ElectroTechnique/TSynth-Teensy4.1/TSynth/effect_envelope.cpp

/* Audio Library for Teensy 3.X
 * Portions Copyright (c) 2017, Paul Stoffregen, paul@pjrc.com
 * Portions Copyright (c) 2021 Vince R. Pearson
 *
 * Development of this audio library was funded by PJRC.COM, LLC by sales of
 * Teensy and Audio Adaptor boards.  Please support PJRC's efforts to develop
 * open source software by purchasing Teensy or other PJRC products.
 *
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
 * THE SOFTWARE IS PROVIDED "AS IS", WITHOUT WARRANTY OF ANY KIND, EXPRESS OR
 * IMPLIED, INCLUDING BUT NOT LIMITED TO THE WARRANTIES OF MERCHANTABILITY,
 * FITNESS FOR A PARTICULAR PURPOSE AND NONINFRINGEMENT. IN NO EVENT SHALL THE
 * AUTHORS OR COPYRIGHT HOLDERS BE LIABLE FOR ANY CLAIM, DAMAGES OR OTHER
 * LIABILITY, WHETHER IN AN ACTION OF CONTRACT, TORT OR OTHERWISE, ARISING FROM,
 * OUT OF OR IN CONNECTION WITH THE SOFTWARE OR THE USE OR OTHER DEALINGS IN
 * THE SOFTWARE.
 */

#include <Arduino.h>
#include "effect_envelope.h"


#define RELEASE_BIAS 256 // based on a 1.31 fixed point integer. This is the level below zero that is the release target and causes the output to go to zero earlier. Otherwise it can take a relatively long time.
// Difference equation for exponential envelope.
#define FORCED_RELEASE_BIAS 0x1000000 // empirically determined with forced release time constant to attain ~5ms between forced release and next attack.
// Form 1 for attack stage: y(n+1) = k1*y(n)+kx using unsigned S1.30 fixed point format
#define EXP_ENV_FILT1(k,y,x) ((uint32_t)(((uint64_t)(y)*(k))>>30)+(uint32_t)(x))
// Form 2 for remaining stages: y(n+1) = k1*(y(n)-x(n))+x(n) using unsigned S1.30 fixed point format
#define EXP_ENV_FILT2(k,y,x) ((((int64_t)(k)*(int64_t)(y-x))>>30)+(x))
#define YSUM2MULT(x) ((x)>>14)

void AudioEffectEnvelopeTS::noteOn(void)
{
  __disable_irq();
  if(release_forced_count==0)
    state=STATE_IDLE;
  switch(state)
  {

    case STATE_IDLE:
    case STATE_IDLE_NEXT:
      // In a corner case, where the state becomes STATE_IDLE EXACTLY at the end of an update(),
	  // AND noteOn() is called before the next update() occurs, AND delay_count is non-zero, 
	  // AND the exponential envelope shape is in use, exp_count will have a stale value 
	  // of 2^32-1 and the delay becomes about 9 days. So duplicate some code here - it
	  // might be possible to move it instead
      exp_count=((uint32_t)(delay_count))*8;
      ysum=0;
	  
      count=delay_count;
      if(count>0)
      {
        state=STATE_DELAY;
        inc_hires=0;
      }
      else
      {
        state=STATE_ATTACK;
        count=attack_count;
      inc_hires = 0x40000000 / (int32_t)count;
      }
      break;    
    case STATE_DELAY:
    case STATE_HOLD:
    case STATE_ATTACK:
    case STATE_DECAY:
    case STATE_SUSTAIN:
    case STATE_SUSTAIN_FAST_CHANGE:
    case STATE_RELEASE:
      state=STATE_FORCED;
      count=release_forced_count;
      inc_hires=(-mult_hires)/(int32_t)count;
    case STATE_FORCED:
      break;
    default:
      state=STATE_RELEASE;
      break;
  }
  __enable_irq();
}

void AudioEffectEnvelopeTS::noteOff(void)
{
  __disable_irq();
  switch(state)
  {
    case STATE_IDLE:
    case STATE_IDLE_NEXT:
    case STATE_DELAY:
      state=STATE_IDLE;
      break;
    default:
      state = STATE_RELEASE;
      count = release_count;
      inc_hires = (-mult_hires) / (int32_t)count;
  }
  __enable_irq();
}

void AudioEffectEnvelopeTS::update(void)
{
  audio_block_t *block;
  uint32_t *p, *end;
  uint32_t sample12, sample34, sample56, sample78, tmp1, tmp2;
  uint32_t exp_mult[8];

  block = receiveWritable();
  if (!block) return;
  if (state == STATE_IDLE) {
    release(block);
    return;
  }
  p = (uint32_t *)(block->data);
  end = p + AUDIO_BLOCK_SAMPLES/2;
  if(env_type==-128)
  { // Original AudioEffectEnvelope class linear envelope.
    while (p < end) {
      // we only care about the state when completing a region
      if (count == 0) {
        if (state == STATE_ATTACK) {
          count = hold_count;
          if (count > 0) {
            state = STATE_HOLD;
            mult_hires = 0x40000000;
            inc_hires = 0;
          } else {
            state = STATE_DECAY;
            count = decay_count;
            inc_hires = (sustain_mult - 0x40000000) / (int32_t)count;
          }
          continue;
        } else if (state == STATE_HOLD) {
          state = STATE_DECAY;
          count = decay_count;
          inc_hires = (sustain_mult - 0x40000000) / (int32_t)count;
          continue;
        } else if (state == STATE_DECAY) {
          state = STATE_SUSTAIN;
          count = 0xFFFF;
          mult_hires = sustain_mult;
          inc_hires = 0;
        } else if (state == STATE_SUSTAIN) {
          count = 0xFFFF;
        } else if (state == STATE_RELEASE) {
          state = STATE_IDLE;
          while (p < end) {
            *p++ = 0;
            *p++ = 0;
            *p++ = 0;
            *p++ = 0;
          }
          break;
        } else if (state == STATE_FORCED) {
          mult_hires = 0;
          count = delay_count;
          if (count > 0) {
            state = STATE_DELAY;
            inc_hires = 0;
          } else {
            state = STATE_ATTACK;
            count = attack_count;
            inc_hires = 0x40000000 / (int32_t)count;
          }
        } else if (state == STATE_DELAY) {
          state = STATE_ATTACK;
          count = attack_count;
          inc_hires = 0x40000000 / count;
          continue;
        }
        else
        {
          state=STATE_IDLE; // If in some unused state switching back into linear mode, set to known state that linear mode uses.
          count=delay_count;
        }
      }

      int32_t mult = mult_hires >> 14;
      int32_t inc = inc_hires >> 17;
      // process 8 samples, using only mult and inc (16 bit resolution)
      sample12 = *p++;
      sample34 = *p++;
      sample56 = *p++;
      sample78 = *p++;
      p -= 4;
      mult += inc;
      tmp1 = signed_multiply_32x16b(mult, sample12);
      mult += inc;
      tmp2 = signed_multiply_32x16t(mult, sample12);
      sample12 = pack_16b_16b(tmp2, tmp1);
      mult += inc;
      tmp1 = signed_multiply_32x16b(mult, sample34);
      mult += inc;
      tmp2 = signed_multiply_32x16t(mult, sample34);
      sample34 = pack_16b_16b(tmp2, tmp1);
      mult += inc;
      tmp1 = signed_multiply_32x16b(mult, sample56);
      mult += inc;
      tmp2 = signed_multiply_32x16t(mult, sample56);
      sample56 = pack_16b_16b(tmp2, tmp1);
      mult += inc;
      tmp1 = signed_multiply_32x16b(mult, sample78);
      mult += inc;
      tmp2 = signed_multiply_32x16t(mult, sample78);
      sample78 = pack_16b_16b(tmp2, tmp1);
      *p++ = sample12;
      *p++ = sample34;
      *p++ = sample56;
      *p++ = sample78;
      // adjust the long-term gain using 30 bit resolution (fix #102)
      // https://github.com/PaulStoffregen/Audio/issues/102
      mult_hires += inc_hires;
      count--;
    }
  }
  else  //Exponential ADSR Vince R. Pearson
  {
    uint16_t i;
    while (p < end) 
    {
      for(i=0;i<8;i++)
      {
        switch(state)
        {
          case STATE_IDLE:
            // Since delay counts may not necessarily start at aligned boundaries of 8 samples,
            // the loop count has to be multiplied by 8
            // and counted down in the for loop, not in the while loop.
            exp_count=((uint32_t)(delay_count))*8;
            ysum=0;
            state=STATE_IDLE_NEXT; // Do this so reinitialization is only done once at every idle state.
            // Falls through to STATE_IDLE_NEXT
            
          case STATE_IDLE_NEXT:
            break; //ysum is zero here
            
          case STATE_DELAY:
            if(exp_count--) break; // ysum is zero here
            state=STATE_ATTACK;
            break;
            
          case STATE_ATTACK:
            ysum=EXP_ENV_FILT1(attack_k,ysum,attack_target);
            if(ysum>=EXP_ENV_ONE)  
            {   // The maximum 32 bit value of the envelope has been reached.
              ysum=EXP_ENV_ONE;
              if(hold_count)
              {
                exp_count=((uint32_t)hold_count)*8;
                state=STATE_HOLD;
              }
              else 
              {
                state=STATE_DECAY;
                exp_count=((uint32_t)delay_count)*8; // Only used to arbitrarioly define where sustain begins.
              }
            }
            break;
            
          case STATE_HOLD:
            if((exp_count--)==0) 
            {
               state=STATE_DECAY; // ysum is maximum here (ENV_MAX_32).
               exp_count=((uint32_t)delay_count)*8;
            }
            break;
            
          case STATE_DECAY:
            if((exp_count--)==0) state=STATE_SUSTAIN;
            // Sustain is only needed to support isRelease(). This happens after delay_count is decremented to zero.
            // The point at which sustain begins after the start of decay is arbitrary on an exponential curve
            // Here it occurs after one time constant (delay_count*8) which is 63.2% down the decay curve.
            ysum=EXP_ENV_FILT2(decay_k,ysum,sustain_mult);
            break;
            
          case STATE_SUSTAIN: // Gets here from decay when delay count is zero. Used to flag when sustain begins.
            ysum=EXP_ENV_FILT2(decay_k,ysum,sustain_mult);
            break;
            
          case STATE_SUSTAIN_FAST_CHANGE: // Only gets here when sustain is changed while in decay or any sustain states.
            ysum=EXP_ENV_FILT2(FAST_SUSTAIN_K1,ysum,sustain_mult);
            break;
            
          case STATE_RELEASE:
            ysum=EXP_ENV_FILT2(release_k,ysum,-RELEASE_BIAS);
            if(ysum<0) ysum=0;
            // Bias added to end release a bit sooner. Value must be checked for underflow since unsigned integers are used.
            // This has affects the longest release settings the most since it is not scaled with the release time constant.
            if(YSUM2MULT(ysum)==0) // All of the useful bits are zero so no reason to stay in this state.
              state=STATE_IDLE;
            break;
            
          case STATE_FORCED:            
            ysum=EXP_ENV_FILT2(release_forced_k,ysum,-FORCED_RELEASE_BIAS);
            if(YSUM2MULT(ysum)<=0)
            { 
              state=STATE_ATTACK;// revert to IDLE state when useful bits are zero.
              ysum=0;
            }
          default:
            break;  
        }
        exp_mult[i]=YSUM2MULT(ysum);
      }
      // multiply audio samples with 8 envelope samples
      sample12 = *p++;
      sample34 = *p++;
      sample56 = *p++;
      sample78 = *p++;
      p -= 4;
      tmp1 = signed_multiply_32x16b(exp_mult[0], sample12);
      tmp2 = signed_multiply_32x16t(exp_mult[1], sample12);
      sample12 = pack_16b_16b(tmp2, tmp1);
      tmp1 = signed_multiply_32x16b(exp_mult[2], sample34);
      tmp2 = signed_multiply_32x16t(exp_mult[3], sample34);
      sample34 = pack_16b_16b(tmp2, tmp1);
      tmp1 = signed_multiply_32x16b(exp_mult[4], sample56);
      tmp2 = signed_multiply_32x16t(exp_mult[5], sample56);
      sample56 = pack_16b_16b(tmp2, tmp1);
      tmp1 = signed_multiply_32x16b(exp_mult[6], sample78);
      tmp2 = signed_multiply_32x16t(exp_mult[7], sample78);
      sample78 = pack_16b_16b(tmp2, tmp1);
      *p++ = sample12;
      *p++ = sample34;
      *p++ = sample56;
      *p++ = sample78;
    }
  }
  transmit(block);
  release(block);
}

bool AudioEffectEnvelopeTS::isActive()
{
  uint8_t current_state = *(volatile uint8_t *)&state;
  if ((current_state == STATE_IDLE)|| (current_state==STATE_IDLE_NEXT)) return false; // Added STATE_IDLE_NEXT. VRP
  return true;
}

bool AudioEffectEnvelopeTS::isSustain()
{
  uint8_t current_state = *(volatile uint8_t *)&state;
  if (current_state == STATE_SUSTAIN || current_state==STATE_SUSTAIN_FAST_CHANGE) return true;
  return false;
}
 
