ElectroTechnique/TSynth-Teensy4.1/TSynth/Yeysk16pt7b.h

const uint8_t Yeysk16pt7bBitmaps[] PROGMEM = {
  0x00, 0xFF, 0xFF, 0xFF, 0xFF, 0xFF, 0x30, 0x00, 0x00, 0x00, 0x00, 0x00,
  0x00, 0x1C, 0x61, 0x86, 0x0C, 0x18, 0x30, 0x60, 0xC1, 0x83, 0x06, 0x0C,
  0x18, 0x30, 0x60, 0xC1, 0x83, 0x06, 0x0C, 0x18, 0x30, 0x60, 0xC1, 0x83,
  0x06, 0x0C, 0x0C, 0x0C, 0x0F, 0xF0, 0x30, 0x30, 0x30, 0x60, 0xC1, 0x83,
  0x06, 0x0C, 0x18, 0x30, 0x60, 0xC1, 0x83, 0x06, 0x0C, 0x18, 0x30, 0x60,
  0xC1, 0x83, 0x06, 0x0C, 0x18, 0x30, 0x61, 0x86, 0x78, 0x00, 0x00, 0xFF,
  0xC0, 0x00, 0xC0, 0x00, 0x0F, 0xFF, 0x81, 0x80, 0x07, 0x18, 0x00, 0x0C,
  0xC0, 0x00, 0x6C, 0x00, 0x01, 0xE0, 0x00, 0x0F, 0x00, 0x00, 0x78, 0x00,
  0x03, 0xC0, 0x00, 0x1E, 0x00, 0x00, 0xF0, 0x00, 0x07, 0x80, 0x00, 0x3C,
  0x00, 0x01, 0xE0, 0x00, 0x0F, 0x00, 0x00, 0x78, 0x00, 0x03, 0xC0, 0x00,
  0x1E, 0x00, 0x00, 0xD8, 0x00, 0x0C, 0xC0, 0x00, 0x63, 0x00, 0x0E, 0x07,
  0xFF, 0xC0, 0xFE, 0x03, 0x03, 0x03, 0x03, 0x03, 0x03, 0x03, 0x03, 0x03,
  0x03, 0x03, 0x03, 0x03, 0x03, 0x03, 0x03, 0x03, 0x03, 0x03, 0x03, 0x03,
  0x0F, 0xFF, 0xE0, 0xE0, 0x00, 0xC6, 0x00, 0x01, 0x98, 0x00, 0x03, 0xC0,
  0x00, 0x0F, 0x00, 0x00, 0x3C, 0x00, 0x00, 0xC0, 0x00, 0x03, 0x00, 0x00,
  0x0C, 0x00, 0x00, 0x30, 0x00, 0x00, 0xC0, 0x00, 0x06, 0x00, 0x00, 0x30,
  0x3F, 0xFF, 0x83, 0x80, 0x00, 0x18, 0x00, 0x00, 0xE0, 0x00, 0x03, 0x00,
  0x00, 0x0C, 0x00, 0x00, 0x30, 0x00, 0x00, 0xC0, 0x00, 0x03, 0xFF, 0xFF,
  0xF0, 0x1F, 0xFF, 0xE0, 0xC0, 0x00, 0xC6, 0x00, 0x01, 0xB0, 0x00, 0x03,
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
  {  1043,  23,  22,  25,    1,  -21 },   // 0x46 'F'
  {  1107,  23,  22,  25,    1,  -21 },   // 0x47 'G'
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

const GFXfont Yeysk16pt7b PROGMEM = {
  (uint8_t  *)Yeysk16pt7bBitmaps,
  (GFXglyph *)Yeysk16pt7bGlyphs,
  0x20, 0x7E, 32 };

// Approx. 4657 bytes https://rop.nl/truetype2gfx/
